VitalyObrubov/PwKeeper2-0/Foto/joystic.jpg

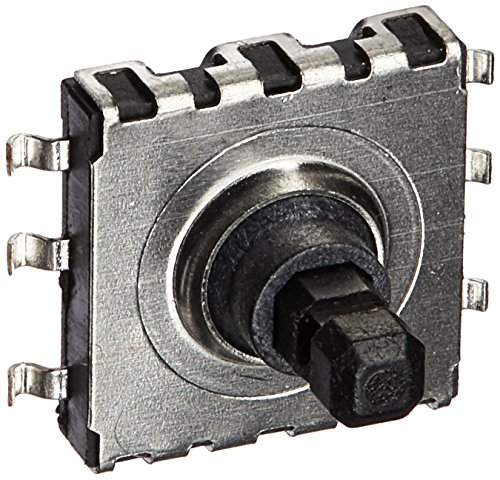
Foto/joystic.jpg
