VitalyObrubov/PwKeeper2-0/Foto/Leonardo Beetle.jpg

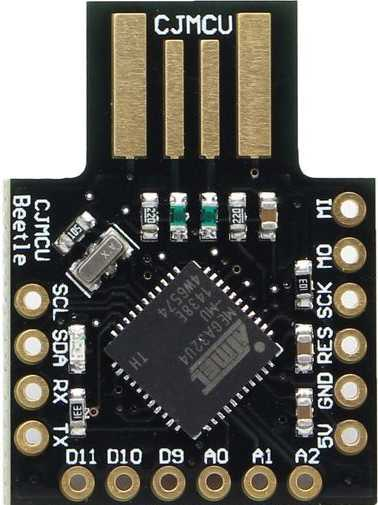
Foto/Leonardo Beetle.jpg
