VitalyObrubov/PwKeeper2-0/Foto/oled.webp

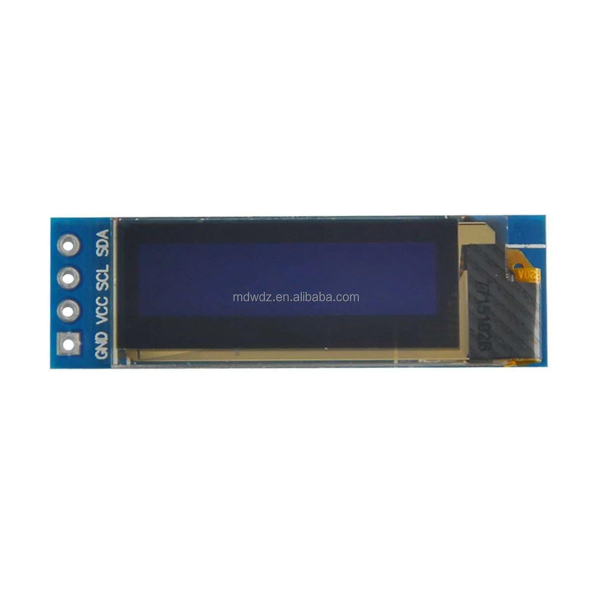
Foto/oled.webp
