VitalyObrubov/PwKeeper2-0/Foto/PwKeeper-bottom.jpg

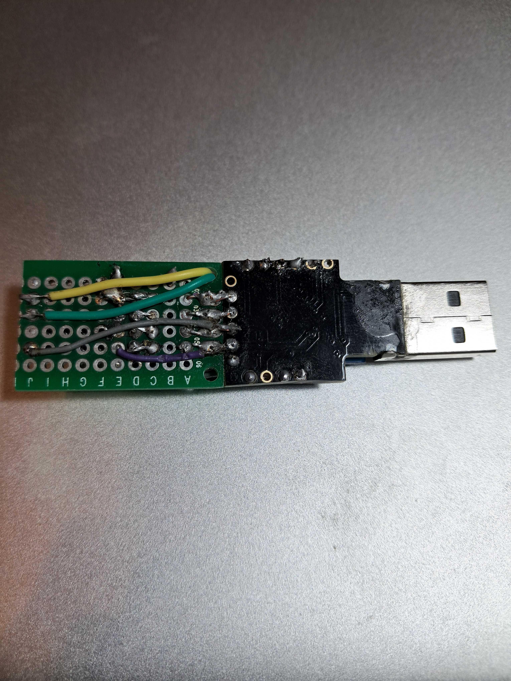
Foto/PwKeeper-bottom.jpg
