VitalyObrubov/PwKeeper2-0/Foto/PwKeeper-work.jpg

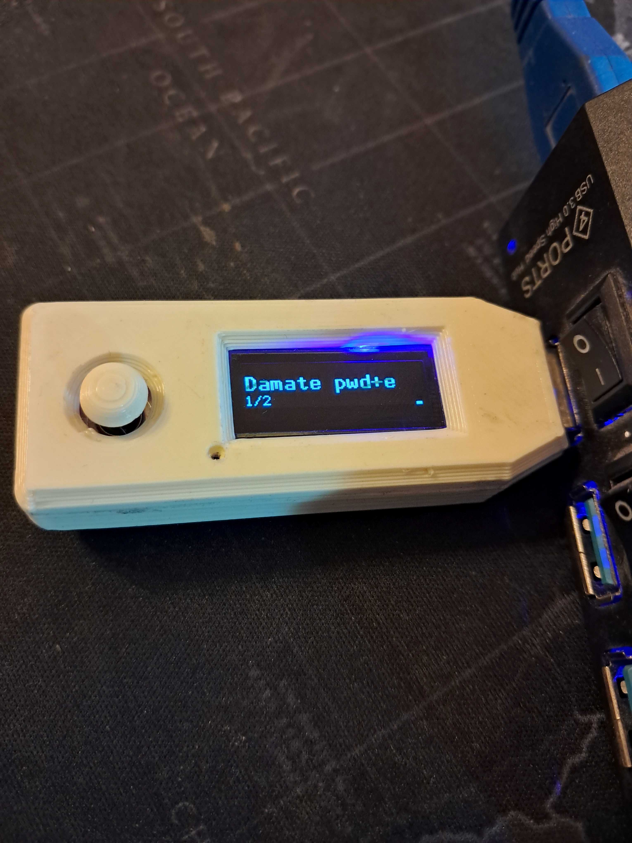
Foto/PwKeeper-work.jpg
