VitalyObrubov/PwKeeper2-0/Foto/МикроДжостик_TMHM14.gif

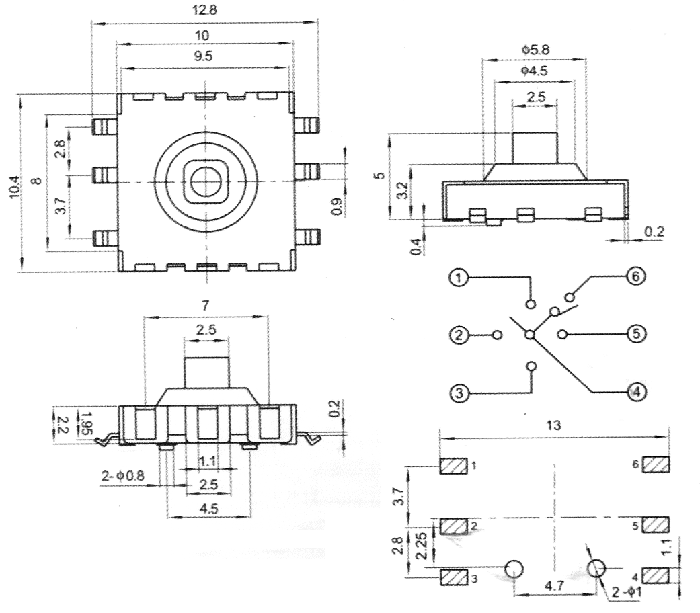
Foto/МикроДжостик_TMHM14.gif
