VitalyObrubov/PwKeeper2-0/Foto/ПростоДырки2х8.jpg

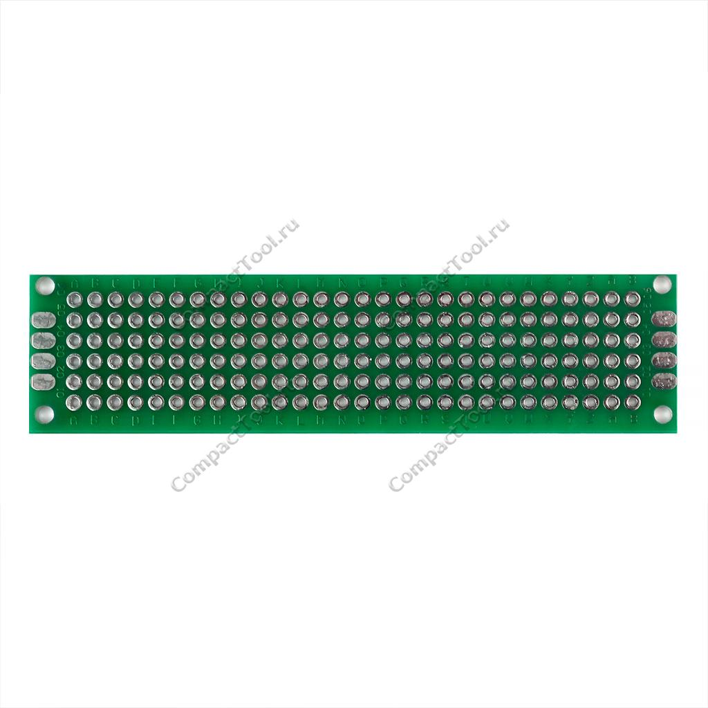
Foto/ПростоДырки2х8.jpg
